joruiz/ap2-graphicdisplay/Firmware/TestPrograms/DebugTest/DebugTest.ino

#define DEBUG1 7
#define DEBUG2 8

#define LED DEBUG2

void setup() {                
  pinMode(LED, OUTPUT);     
}

void loop() {
  digitalWrite(LED, HIGH);   // turn the LED on (HIGH is the voltage level)
  delay(1000);               // wait for a second
  digitalWrite(LED, LOW);    // turn the LED off by making the voltage LOW
  delay(1000);               // wait for a second
}
